jmfb/CustomKeyboard/Images/V5/01_LedSipKeys/05_AddSipSockets.jpeg

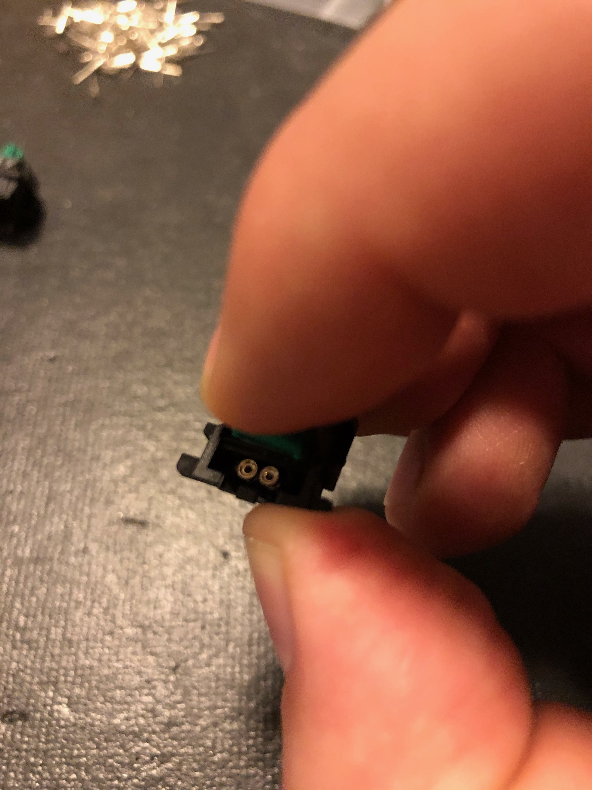
Images/V5/01_LedSipKeys/05_AddSipSockets.jpeg
