jmfb/CustomKeyboard/Images/V5/01_LedSipKeys/06_SipDone.jpeg

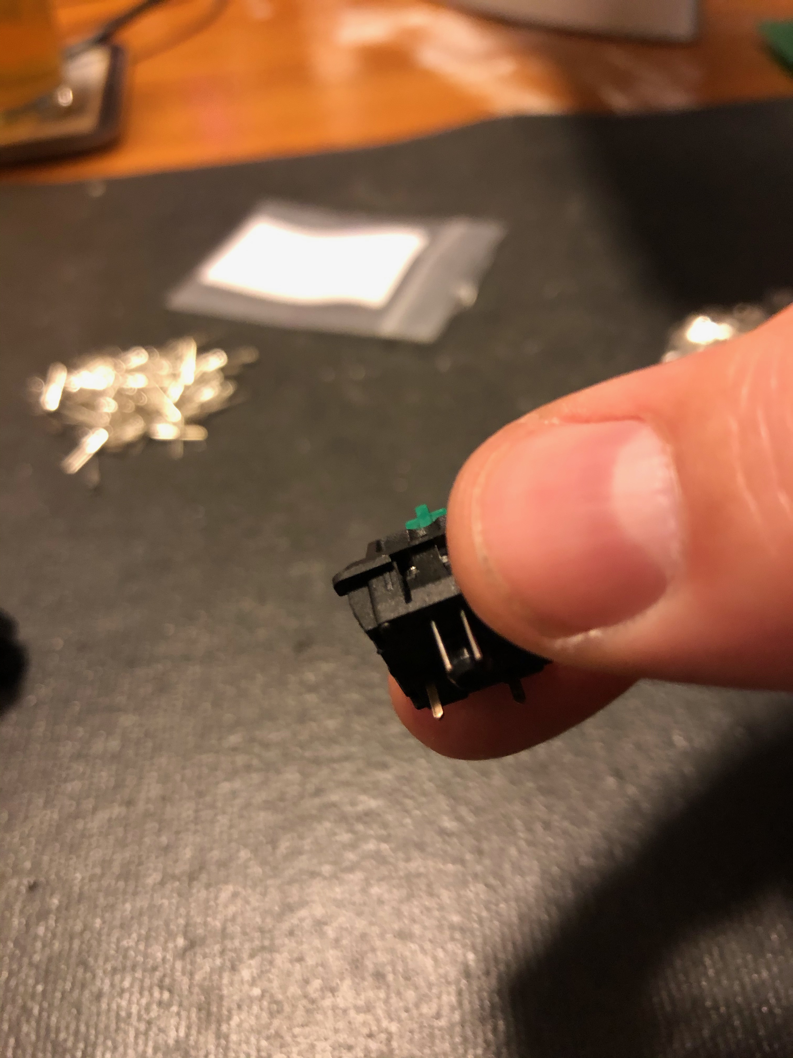
Images/V5/01_LedSipKeys/06_SipDone.jpeg
