jmfb/CustomKeyboard/Images/V5/01_LedSipKeys/08_110SipLedSwitches.jpeg

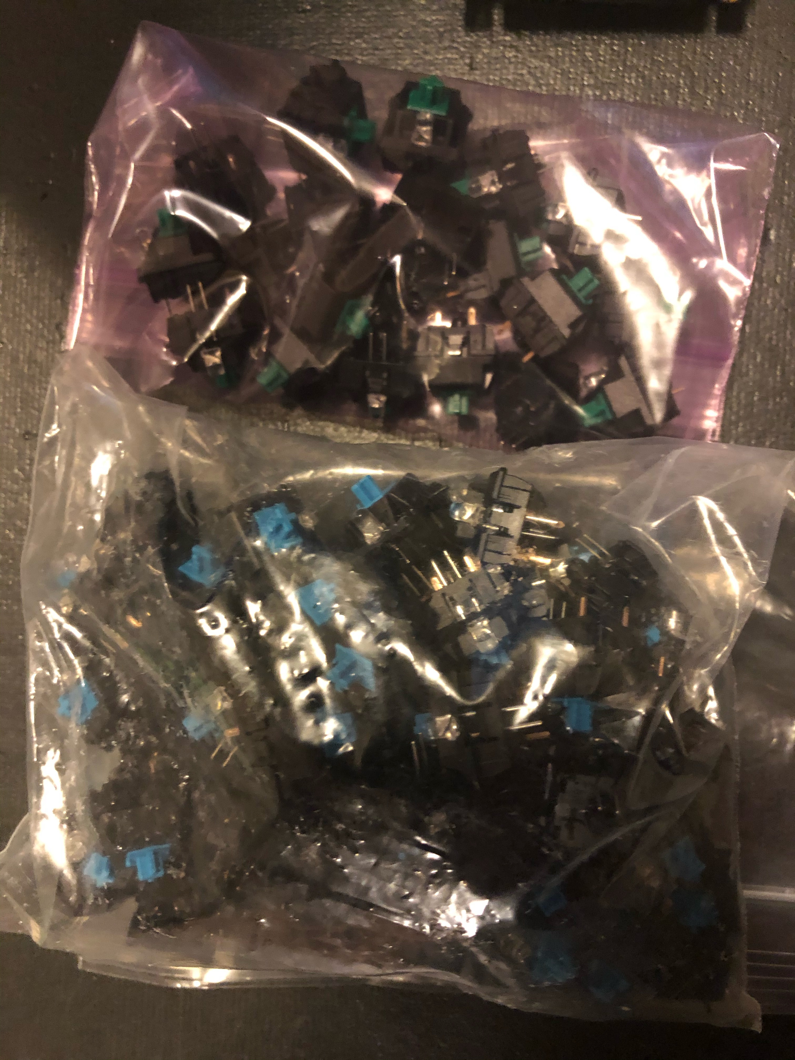
Images/V5/01_LedSipKeys/08_110SipLedSwitches.jpeg
