jmfb/CustomKeyboard/Case/LeftHandTop.stl

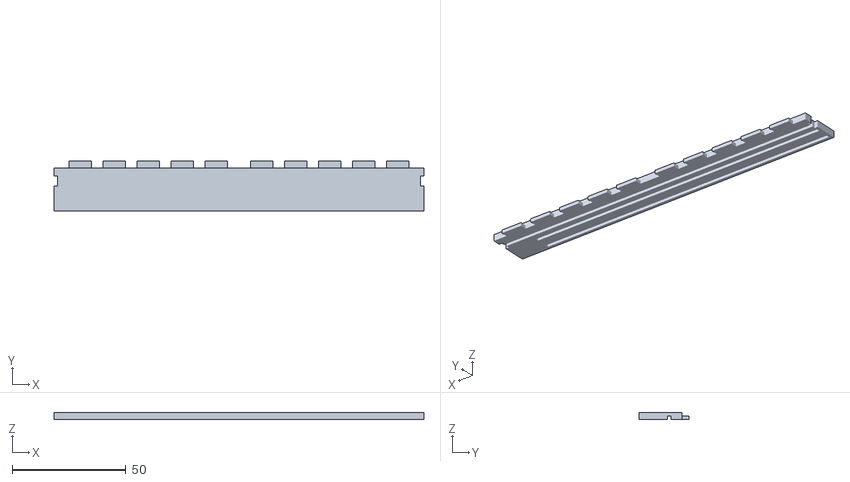
[picture p32: CAD file, 2017-11-25]
Case/LeftHandTop.stl
163.0 x 22.0 x 3.00
