jmfb/CustomKeyboard/FacePlates/Accessory.v2.dxf

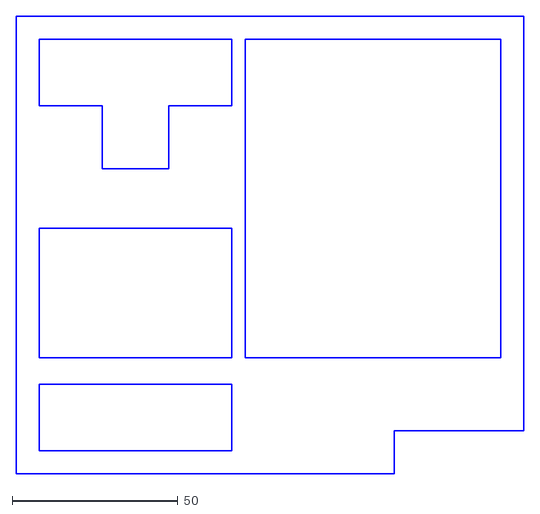
[picture p33: CAD file, 2017-11-25]
FacePlates/Accessory.v2.dxf
153.0 x 138.0
