jmfb/CustomKeyboard/Case/LeftHandLeft.stl

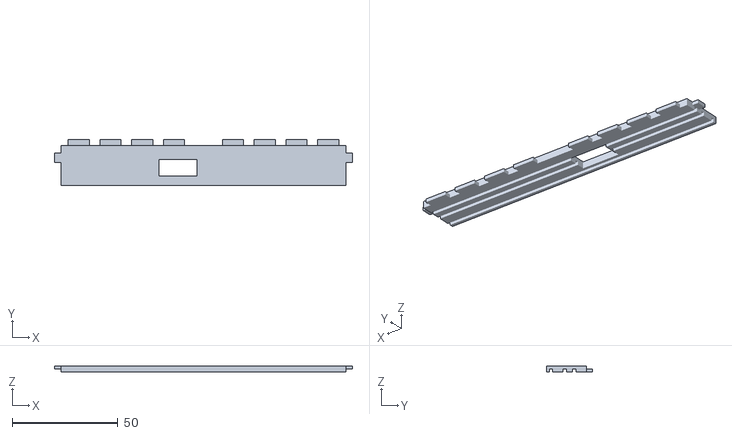
[picture p34: CAD file, 2017-11-25]
Case/LeftHandLeft.stl
141.0 x 22.0 x 3.00
