jmfb/CustomKeyboard/FacePlates/RightHand.v2.dxf

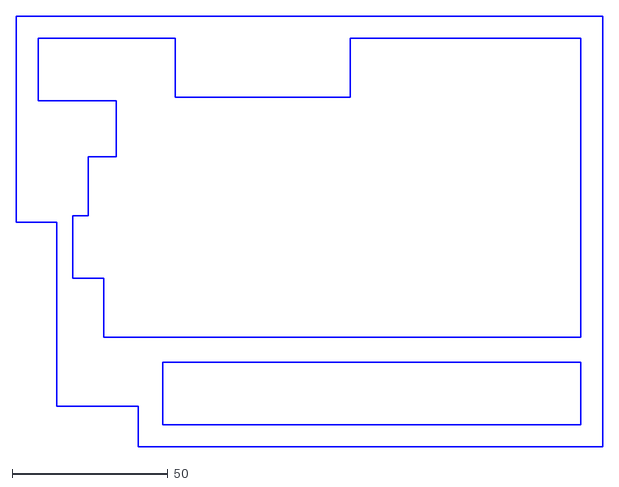
[picture p35: CAD file, 2017-11-25]
FacePlates/RightHand.v2.dxf
188.0 x 138.0
