jmfb/CustomKeyboard/Case/LeftHandRight.stl

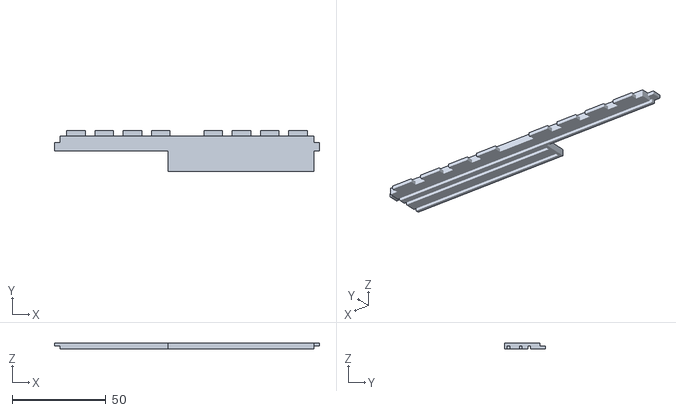
[picture p36: CAD file, 2017-11-25]
Case/LeftHandRight.stl
141.0 x 22.0 x 3.00
