jmfb/CustomKeyboard/FacePlates/LeftHand.v2.dxf

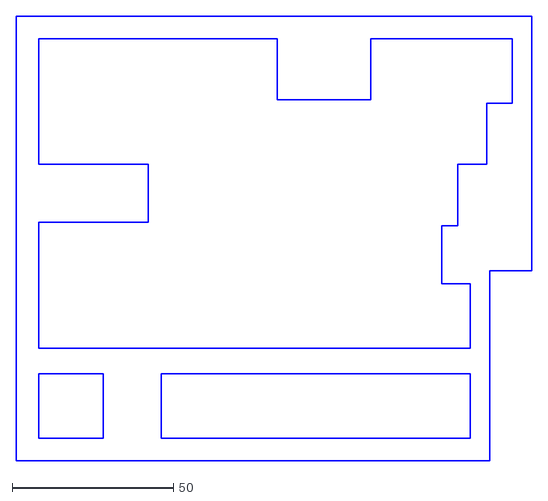
[picture p37: CAD file, 2017-11-25]
FacePlates/LeftHand.v2.dxf
160.0 x 138.0
