jmfb/CustomKeyboard/Case/LeftHandBottom.stl

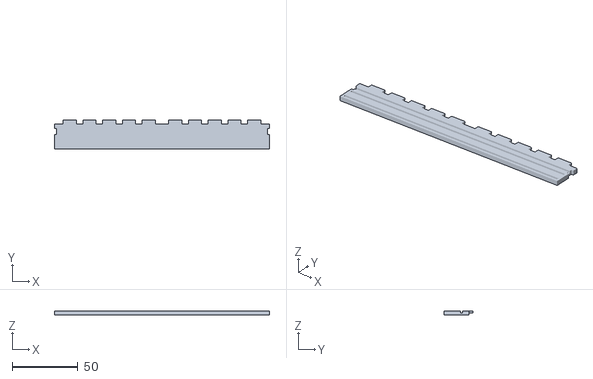
[picture p38: CAD file, 2017-11-25]
Case/LeftHandBottom.stl
163.0 x 22.0 x 3.00
