jmfb/CustomKeyboard/Case/RightHandAndAccessoryRight.scad

board = 138;
edge = 1.5;

depth = 2 * edge;
width = board + 2 * edge;

groove = 1.5;
faceSpace = 5;
mountSpace = 3;
pcbSpace = 5;

notchSpacing = 5;
notchWidth = 10;
notchHeight = 3;

height =
	edge +
	groove +
	faceSpace +
	groove +
	mountSpace +
	groove +
	pcbSpace +
	notchHeight;

faceTop = edge;
mountTop = faceTop + groove + faceSpace;
pcbTop = mountTop + groove + mountSpace;
baseTop = pcbTop + groove + pcbSpace;

notchCount = 8;
notchGap = board - notchCount * (notchSpacing + notchWidth);
notch1Left = edge + notchSpacing;
notch2Left = notch1Left + notchSpacing + notchWidth;
notch3Left = notch2Left + notchSpacing + notchWidth;
notch4Left = notch3Left + notchSpacing + notchWidth;
notch5Left = notch4Left + notchGap + notchWidth;
notch6Left = notch5Left + notchSpacing + notchWidth;
notch7Left = notch6Left + notchSpacing + notchWidth;
notch8Left = notch7Left + notchSpacing + notchWidth;

module hole(x, y, z, cx, cy, cz)
{
	translate([x, y, z]) cube([cx, cy, cz]);
}

module grooveHole(x, y)
{
	hole(edge + x, y, 0, board - x, groove, edge);
}

module notchHole(x, cx)
{
	hole(x, baseTop, 0, cx, notchHeight, edge);
}

module sideNotch(x)
{
	hole(x, 0, 0, 2 * edge, height, edge);
	hole(x, 0, edge, 2 * edge, pcbTop - edge, edge);
	hole(x, pcbTop + 2 * edge, edge, 2 * edge, 2 * edge + groove, edge);
}

difference()
{
	cube([width, height, depth]);

	grooveHole(13, faceTop);
	grooveHole(13, mountTop);
	grooveHole(0, pcbTop);

	hole(0, baseTop, edge, width, notchHeight, edge);
	notchHole(0, notch1Left);
	notchHole(notch1Left + notchWidth, notchSpacing);
	notchHole(notch2Left + notchWidth, notchSpacing);
	notchHole(notch3Left + notchWidth, notchSpacing);
	notchHole(notch4Left + notchWidth, notchGap);
	notchHole(notch5Left + notchWidth, notchSpacing);
	notchHole(notch6Left + notchWidth, notchSpacing);
	notchHole(notch7Left + notchWidth, notchSpacing);
	notchHole(notch8Left + notchWidth, notchSpacing + edge);

	//sideNotch(0);

	hole(0, pcbTop - edge, 0, 2 * edge, height, edge);
//	hole(0, 0, edge, 2 * edge, pcbTop - edge, edge);
	hole(0, pcbTop + 2 * edge, edge, 2 * edge, 2 * edge + groove, edge);

	sideNotch(board);
}
