jmfb/CustomKeyboard/Mini/V3/mini.scad

include <constants.scad>

// Toggle this to include/exclude PCB from model
includePcb = true;

module keySwitch(extraTop, extraBottom) {
	if (includePcb) {
		// PCB footprint
		color("green")
		translate([keyPcbXOffset, 0, 0])
		cube([keyPcbWidth, keyPcbHeight, pcbDepth]);
	}

	translate([0, -extraTop, pcbDepth + pcbMountSpacing])
	difference() {
		// Mounting plate level
		cube([keySize, keySize + extraTop + extraBottom, mountingPlateDepth]);

		// Key hole cutout
		translate([mountingHoleOffset, extraTop + mountingHoleOffset, -epsilon])
		cube([keyHoleSize, keyHoleSize, mountingPlateDepth + 2 * epsilon]);
	}
}

module keyColumn(
	lowerRowMountHeight,
	topRowMountHeight
) {
	// Home row
	keySwitch(homeToTopRowExtension, homeToBottomRowExtension);

	// Bottom row
	translate([0, keySize + pcbBottomSpaceUnderHome, 0])
	rotate([lowerRowAngle, 0, 0])
	translate([0, pcbBottomSpaceAfterLowerBend, 0])
	union() {
		keySwitch(bottomRowToHomeExtension, extraRowExtension);

		// Diagonal wall to vertical edge
		translate([
			0,
			keySize + extraRowExtension - modelWallDepth,
			-minDepthBelowPcb - lowerRowMountHeight + mountHeight
		])
		cube([keySize, modelWallDepth, lowerRowMountHeight]);
	}

	// Top row
	translate([0, -pcbBottomSpaceAboveHome, 0])
	rotate([-upperRowAngle, 0, 0])
	translate([0, -(keySize + pcbBottomSpaceAfterUpperBend), 0])
	union() {
		keySwitch(extraRowExtension, topRowToHomeExtension);

		// Diagonal wall to vertical edge
		translate([
			0,
			-extraRowExtension,
			-minDepthBelowPcb - topRowMountHeight + mountHeight
		])
		cube([keySize, modelWallDepth, topRowMountHeight]);
	}
}

module columnWall(
	topDepth,
	bottomRowWallDistance,
	topRowWallDistance,
	zOffset) {
	largeValue = 100;
	hugeValue = 1000;
	overlap = keySize + halfKeySize;

	difference() {
		union() {
			translate([0, -overlap, -largeValue])
			cube([
				modelWallDepth,
				homeRowLength + 2 * overlap,
				largeValue + topDepth
			]);

			translate([0, homeRowLength, 0])
			rotate([lowerRowAngle, 0, 0])
			translate([0, 0, -largeValue])
			cube([modelWallDepth, bottomRowLength, largeValue + topDepth]);

			rotate([-upperRowAngle, 0, 0])
			translate([0, -topRowLength, -largeValue])
			cube([modelWallDepth, topRowLength, largeValue + topDepth]);
		}

		translate([-epsilon, -(hugeValue / 2), -largeValue - epsilon])
		cube([
			modelWallDepth + 2 * epsilon,
			hugeValue,
			largeValue - distanceToMountingPlateBottom - zOffset + epsilon
		]);

		translate([
			-epsilon,
			bottomRowWallDistance + homeToTopRowExtension,
			-largeValue - epsilon])
		cube([modelWallDepth + 2 * epsilon, largeValue, 2 * largeValue]);

		translate([
			-epsilon,
			-topRowWallDistance + homeToTopRowExtension - largeValue,
			-largeValue - epsilon
		])
		cube([modelWallDepth + 2 * epsilon, largeValue, 2 * largeValue]);
	}
}

module homeRow() {
	// Index finger
	union() {
		keyColumn(
			bottomRowWallMountHeightIndex,
			topRowWallMountHeightIndex);

		// Bottom row wall
		translate([0, bottomRowWallDistanceIndex - modelWallDepth, -minDepthBelowPcb + ringZOffset])
		cube([keySize, modelWallDepth, bottomRowWallHeightIndex - ringZOffset]);

		// Top row wall
		translate([0, -topRowWallDistanceIndex, -minDepthBelowPcb + ringZOffset])
		cube([keySize, modelWallDepth, topRowWallHeightIndex - ringZOffset]);
	}

	// Middle finger
	translate([keySize, -middleYOffset, middleZOffset])
	union() {
		keyColumn(
			bottomRowWallMountHeightMiddle,
			mountHeight);

		// Bottom row wall
		translate([0, bottomRowWallDistanceMiddle - modelWallDepth, -minDepthBelowPcb + middleZOffset])
		cube([keySize, modelWallDepth, bottomRowWallHeightMiddle - middleZOffset]);

		// Top row wall
		translate([0, -topRowWallDistanceMiddle, -minDepthBelowPcb + middleZOffset])
		cube([keySize, modelWallDepth, topRowWallHeightMiddle - middleZOffset]);
	}

	// Ring finger
	translate([2 * keySize, -ringYOffset, ringZOffset])
	union() {
		keyColumn(
			bottomRowWallMountHeightRing,
			topRowWallMountHeightRing);

		// Bottom row wall
		translate([0, bottomRowWallDistanceRing - modelWallDepth, -minDepthBelowPcb])
		cube([keySize, modelWallDepth, bottomRowWallHeightRing]);

		// Top row wall
		translate([0, -topRowWallDistanceRing, -minDepthBelowPcb])
		cube([keySize, modelWallDepth, topRowWallHeightRing]);
	}

	// Pinky finger
	translate([3 * keySize, -pinkyYOffset, pinkyZOffset])
	union() {
		keyColumn(
			mountHeight,
			topRowWallMountHeightPinky);

		// Bottom row wall
		translate([0, bottomRowWallDistancePinky - modelWallDepth, -minDepthBelowPcb + ringZOffset - pinkyZOffset])
		cube([keySize, modelWallDepth, bottomRowWallHeightPinky - ringZOffset + pinkyZOffset]);

		// Top row wall
		translate([0, -topRowWallDistancePinky, -minDepthBelowPcb + ringZOffset - pinkyZOffset])
		cube([keySize, modelWallDepth, topRowWallHeightPinky - ringZOffset + pinkyZOffset]);
	}

	//Pinky plus one column
	translate([4 * keySize + pp1XOffset, -pinkyYOffset, pinkyZOffset])
	union() {
		translate([0, halfKeySize, distanceToMountingPlateBottom + mountingPlateDepth])
		rotate([halfPinkyRowAngle, -pinkyColumnAngle, 0])
		translate([0, 0, -distanceToMountingPlateBottom - mountingPlateDepth])
		keySwitch(0, 0);

		translate([0, halfKeySize, distanceToMountingPlateBottom + mountingPlateDepth])
		rotate([-halfPinkyRowAngle, -pinkyColumnAngle, 0])
		translate([0, -keySize, -distanceToMountingPlateBottom - mountingPlateDepth])
		keySwitch(0, 0);
	}
}

module ringPinkyWallCutout() {
	translate([
		3 * keySize - modelWallDepth / 2,
		-ringYOffset - homeToTopRowExtension,
		ringZOffset + distanceToMountingPlateBottom
	])
	columnWall(
		0,
		bottomRowWallDistanceRing,
		topRowWallDistanceRing,
		minDepthBelowPcb);
}

module ringPinkyWall() {
	difference() {
		translate([
			3 * keySize - modelWallDepth / 2,
			-pinkyYOffset - homeToTopRowExtension,
			pinkyZOffset + distanceToMountingPlateBottom
		])
		columnWall(
			mountingPlateDepth,
			bottomRowWallDistancePinky,
			topRowWallDistancePinky,
			pinkyZOffset - ringZOffset + minDepthBelowPcb);

		translate([-epsilon, 0, 0])
		ringPinkyWallCutout();

		translate([epsilon, 0, 0])
		ringPinkyWallCutout();

		translate([0, 0, -epsilon])
		ringPinkyWallCutout();
	}
}

// Left hand (invert x for Right Hand)
homeRow();
// TODO: This is missing the "diagonal" walls.
ringPinkyWall();
