jmfb/CustomKeyboard/Images/V5/01_LedSipKeys/03_110ClippedLeds.jpeg

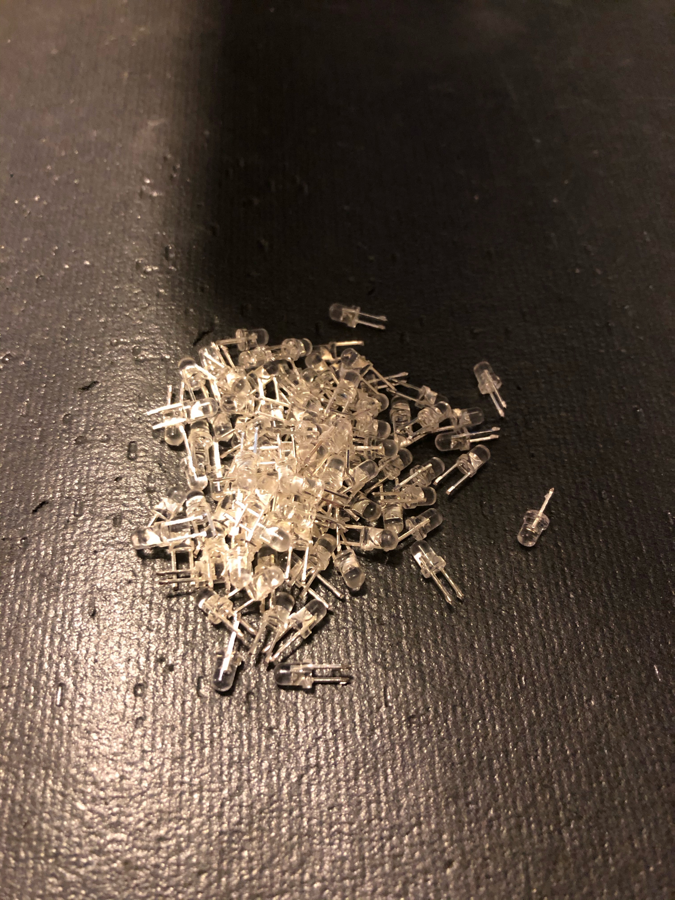
Images/V5/01_LedSipKeys/03_110ClippedLeds.jpeg
