jmfb/CustomKeyboard/Images/V5/01_LedSipKeys/04_OpenSwitch.jpeg

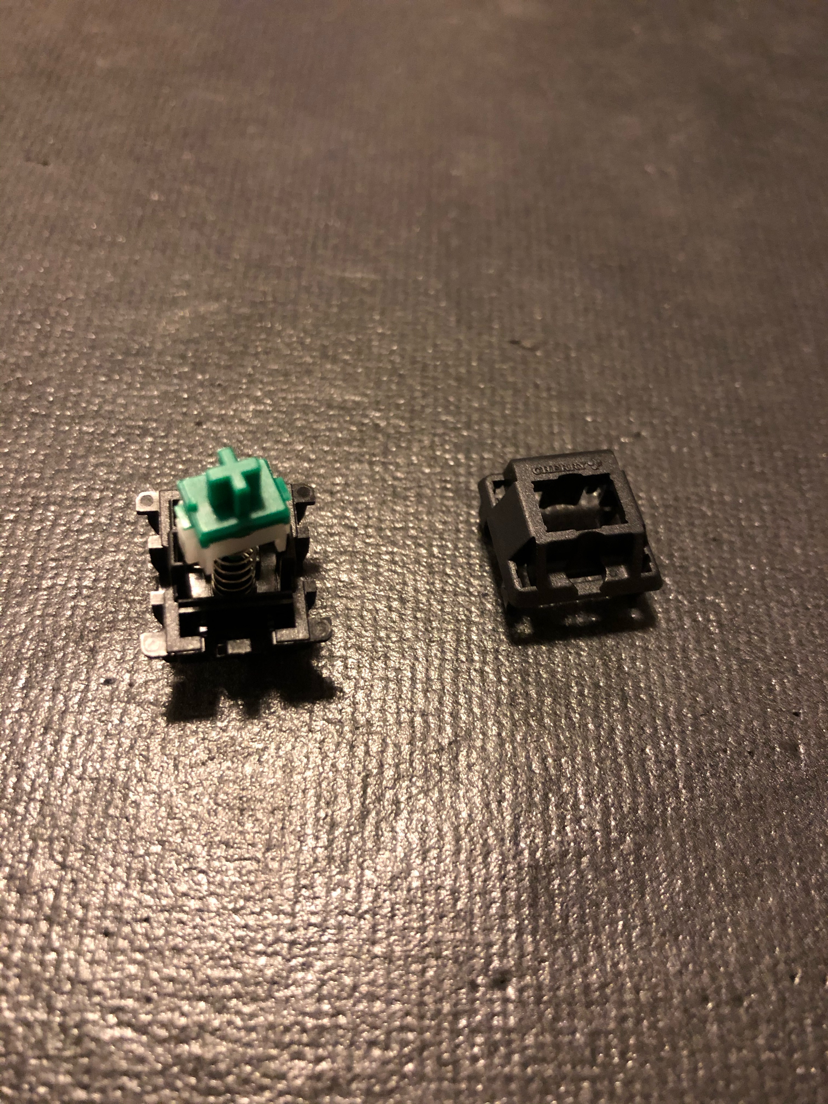
Images/V5/01_LedSipKeys/04_OpenSwitch.jpeg
