jmfb/CustomKeyboard/Images/V5/02_DiodesAndResistors/02_LeftHandBack.jpeg

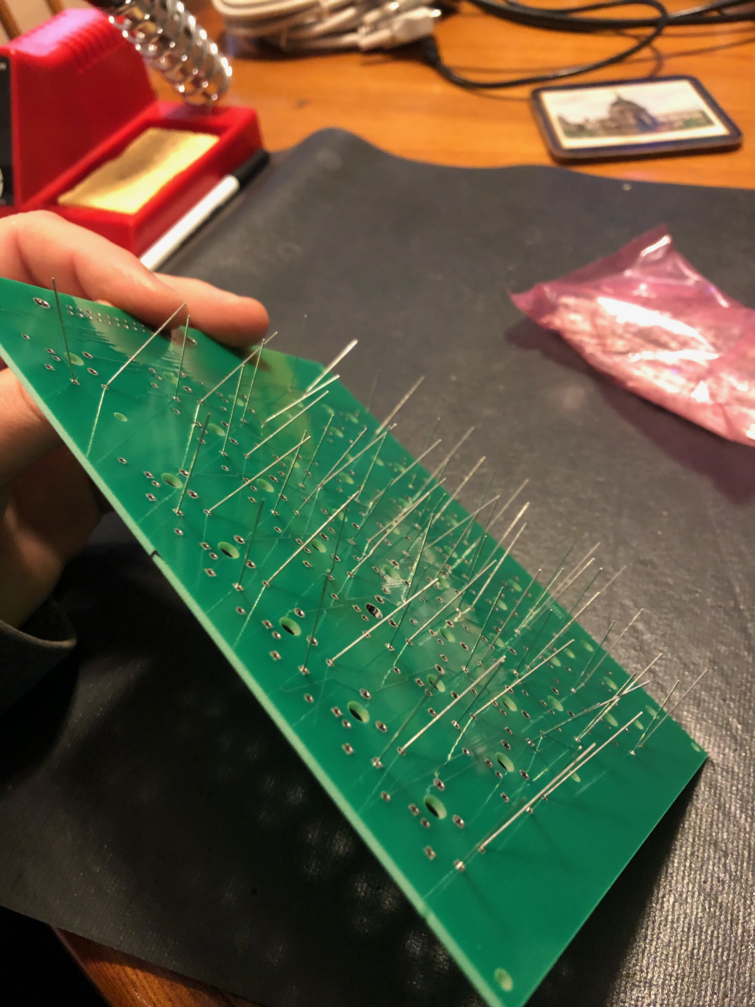
Images/V5/02_DiodesAndResistors/02_LeftHandBack.jpeg
