jmfb/CustomKeyboard/Images/V5/02_DiodesAndResistors/03_RightHandDiodes.jpeg

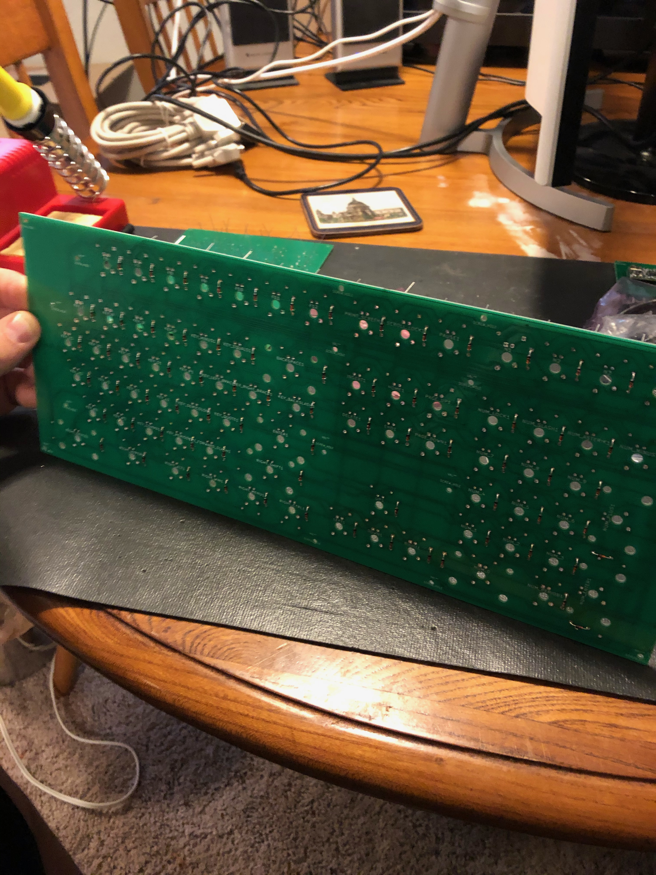
Images/V5/02_DiodesAndResistors/03_RightHandDiodes.jpeg
