jmfb/CustomKeyboard/Images/V5/02_DiodesAndResistors/06_LeftHandBack.jpeg

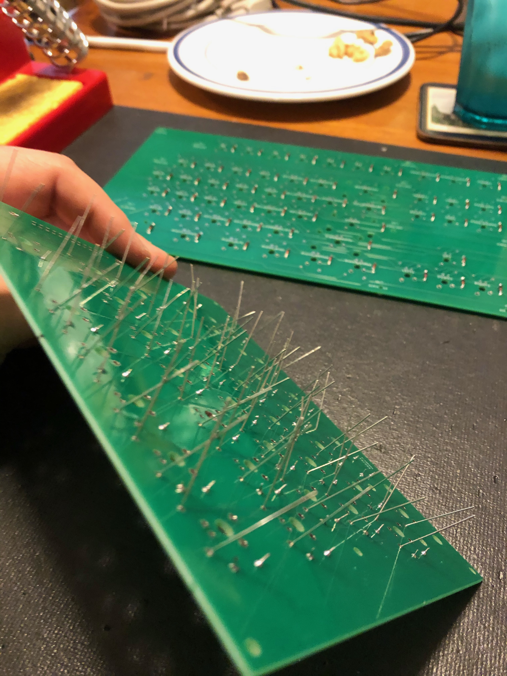
Images/V5/02_DiodesAndResistors/06_LeftHandBack.jpeg
