jmfb/CustomKeyboard/Images/V5/02_DiodesAndResistors/08_RightHandBack.jpeg

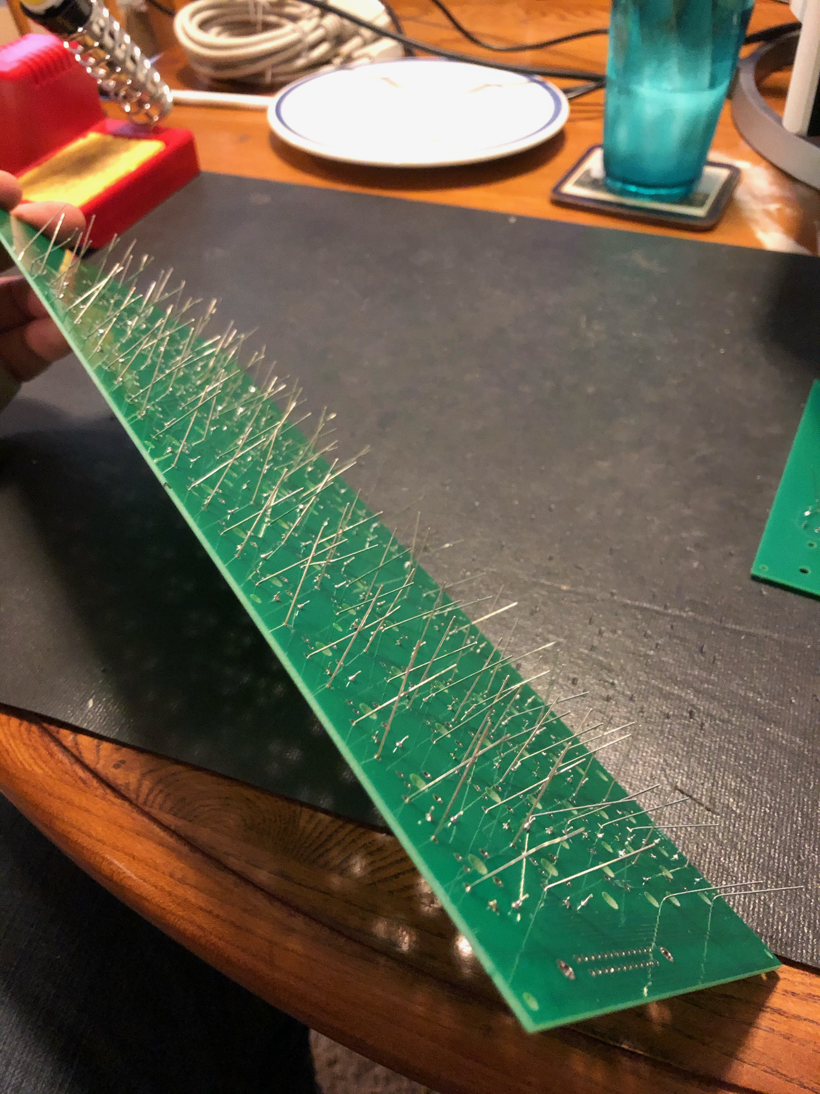
Images/V5/02_DiodesAndResistors/08_RightHandBack.jpeg
