jmfb/CustomKeyboard/Images/V5/02_DiodesAndResistors/09_Dsubs.jpeg

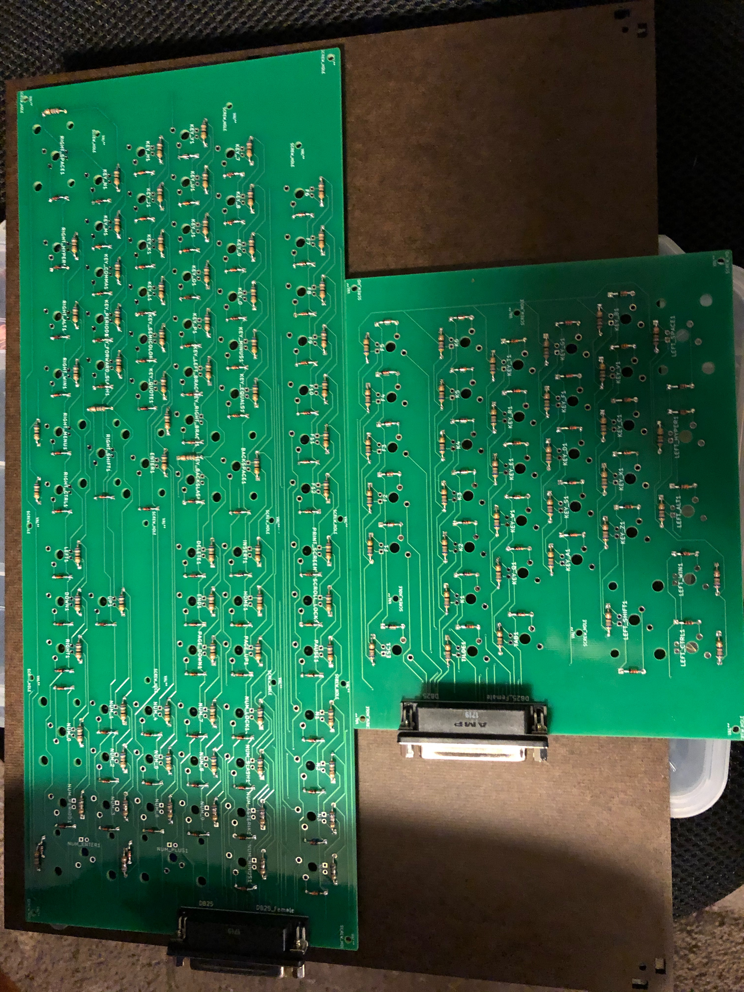
Images/V5/02_DiodesAndResistors/09_Dsubs.jpeg
