jmfb/CustomKeyboard/Images/V5/02_DiodesAndResistors/10_Stabilizers.jpeg

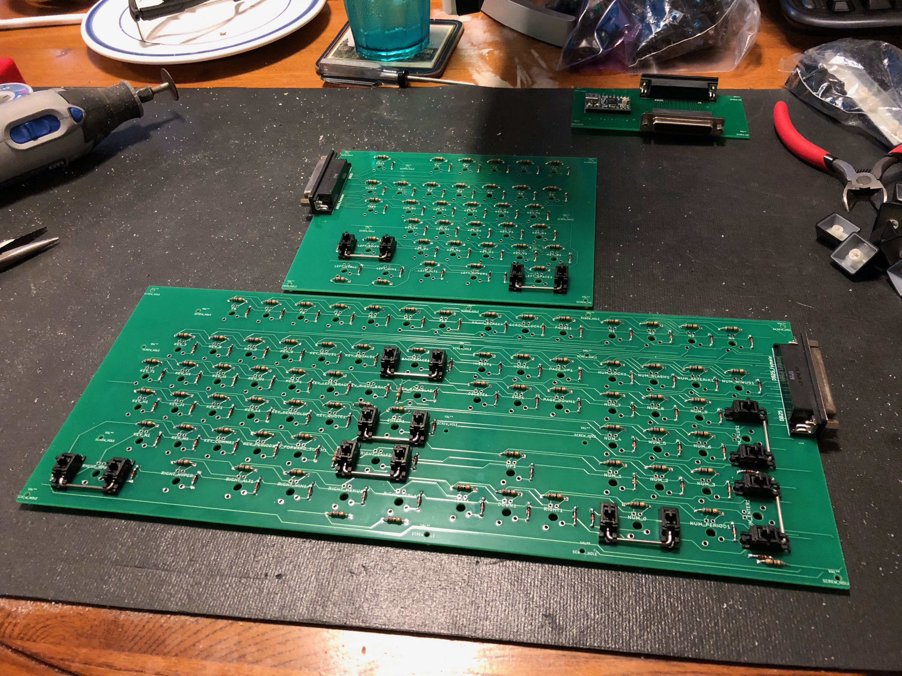
Images/V5/02_DiodesAndResistors/10_Stabilizers.jpeg
